ldab/split-or-not-keyboard/.github/2023-12-31_12-59.png

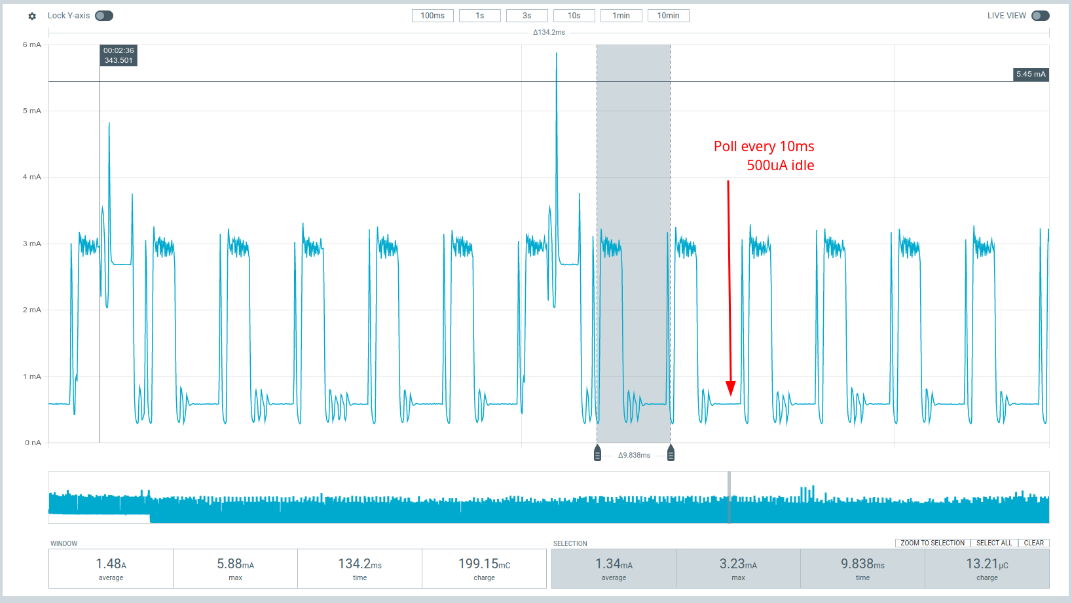
.github/2023-12-31_12-59.png
