ldab/split-or-not-keyboard/.github/basic60_idle_int.png

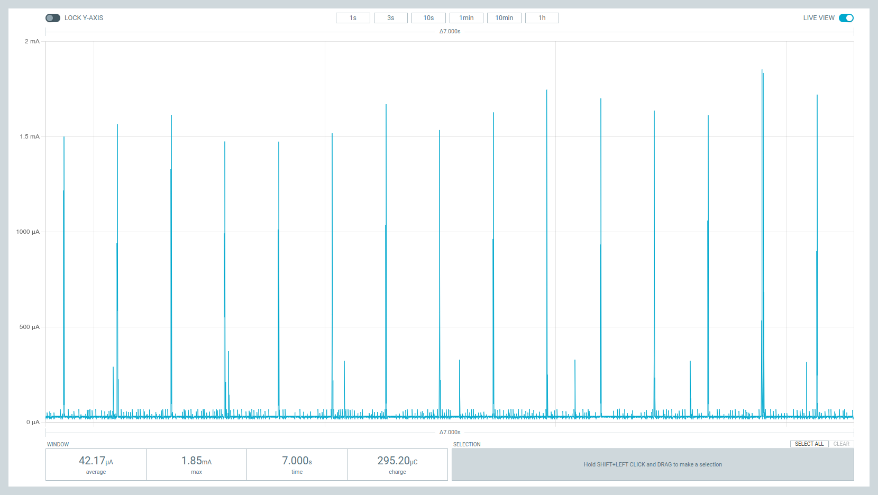
.github/basic60_idle_int.png
