ldab/split-or-not-keyboard/.github/ppk-20240103T102012.png

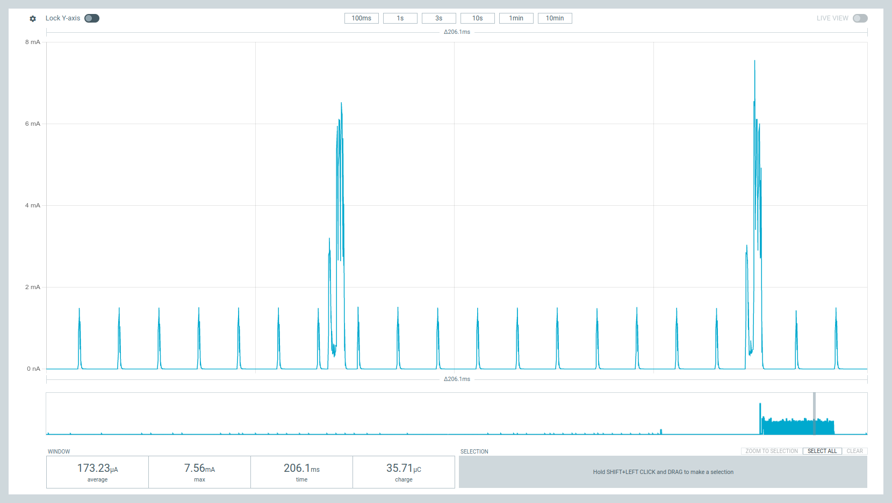
.github/ppk-20240103T102012.png
