ldab/split-or-not-keyboard/.github/ppk-20240103T121507.png

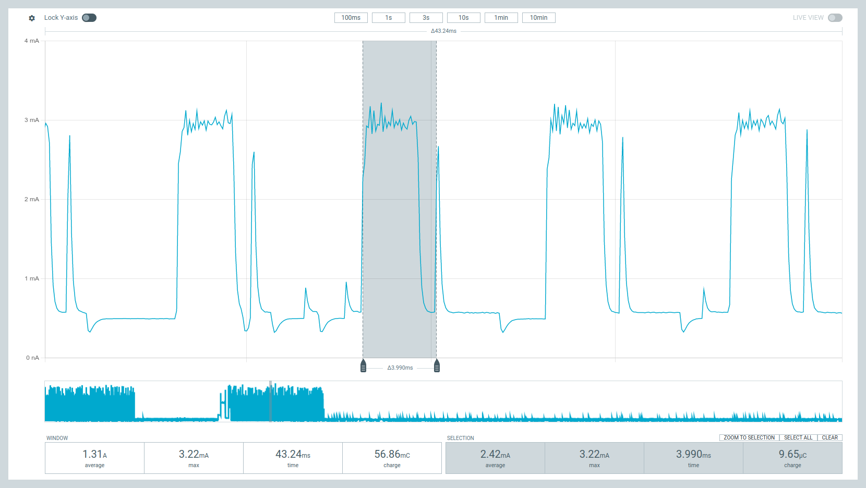
.github/ppk-20240103T121507.png
