ldab/split-or-not-keyboard/basic/3D/basic60-3D_top.png

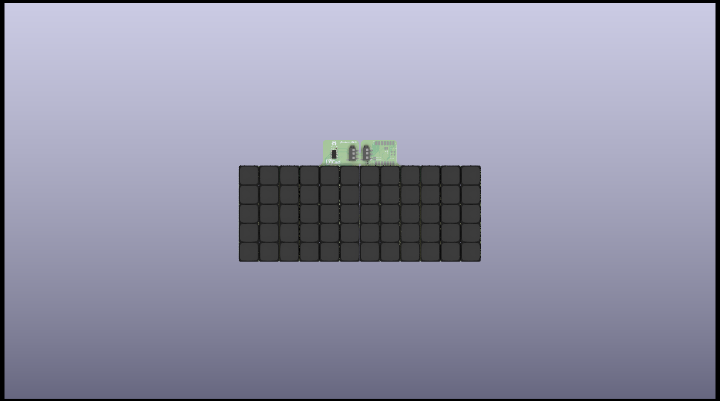
basic/3D/basic60-3D_top.png
