ldab/split-or-not-keyboard/basic/PCB/2D_render/jlcpcb_green_enig/basic60-bottom.png

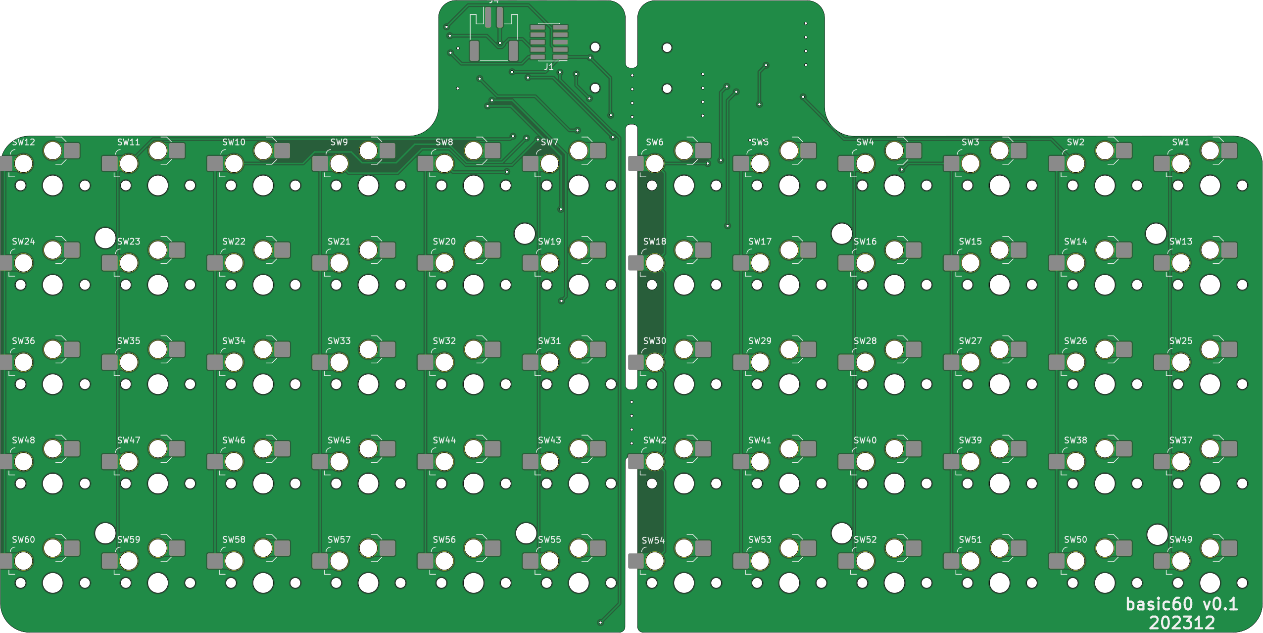
basic/PCB/2D_render/jlcpcb_green_enig/basic60-bottom.png
