ldab/split-or-not-keyboard/ergo/PCB/2D_render/jlcpcb_green_enig/ergo56-bottom.png

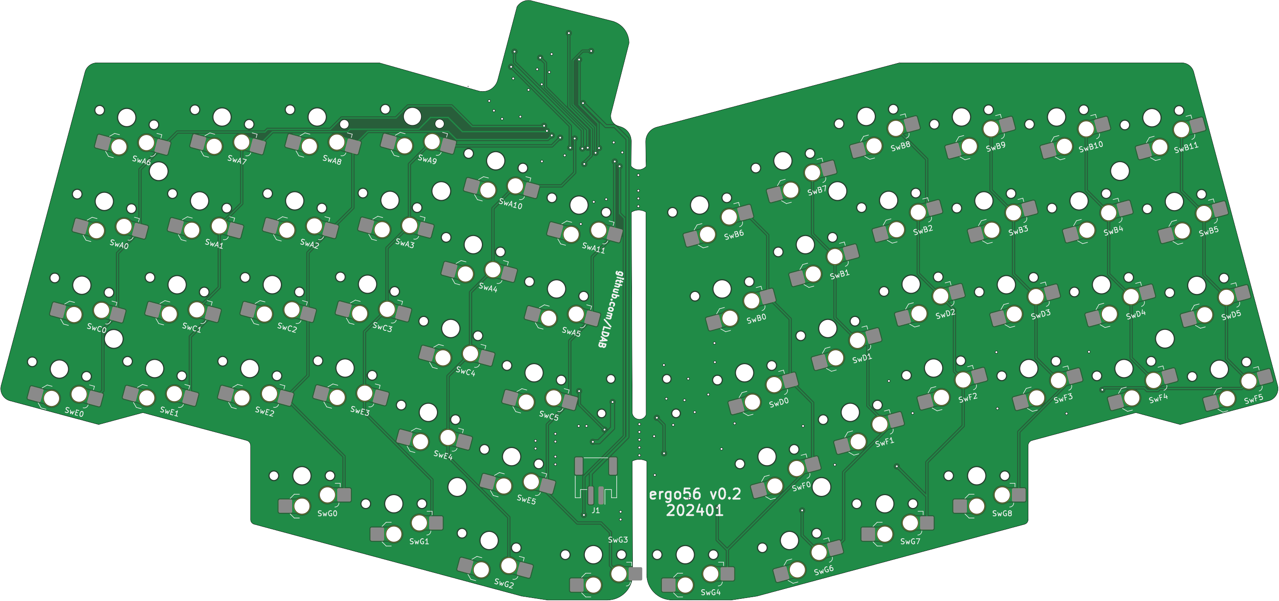
ergo/PCB/2D_render/jlcpcb_green_enig/ergo56-bottom.png
