ldab/split-or-not-keyboard/ergo/PCB/PNG/ergo56-assembly_page_02.png

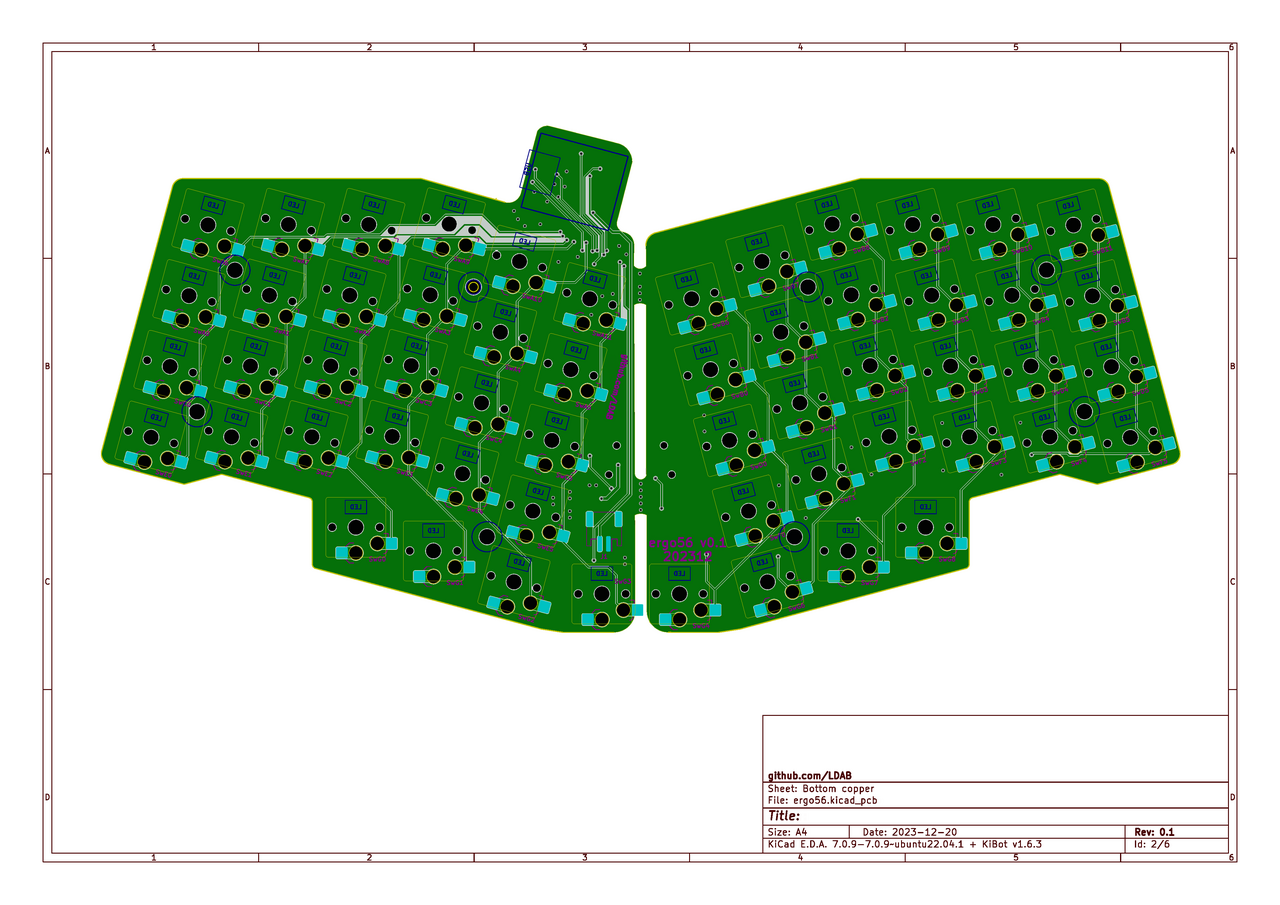
ergo/PCB/PNG/ergo56-assembly_page_02.png
