ldab/split-or-not-keyboard/ergo/PCB/PDF/02/ergo56.pdf

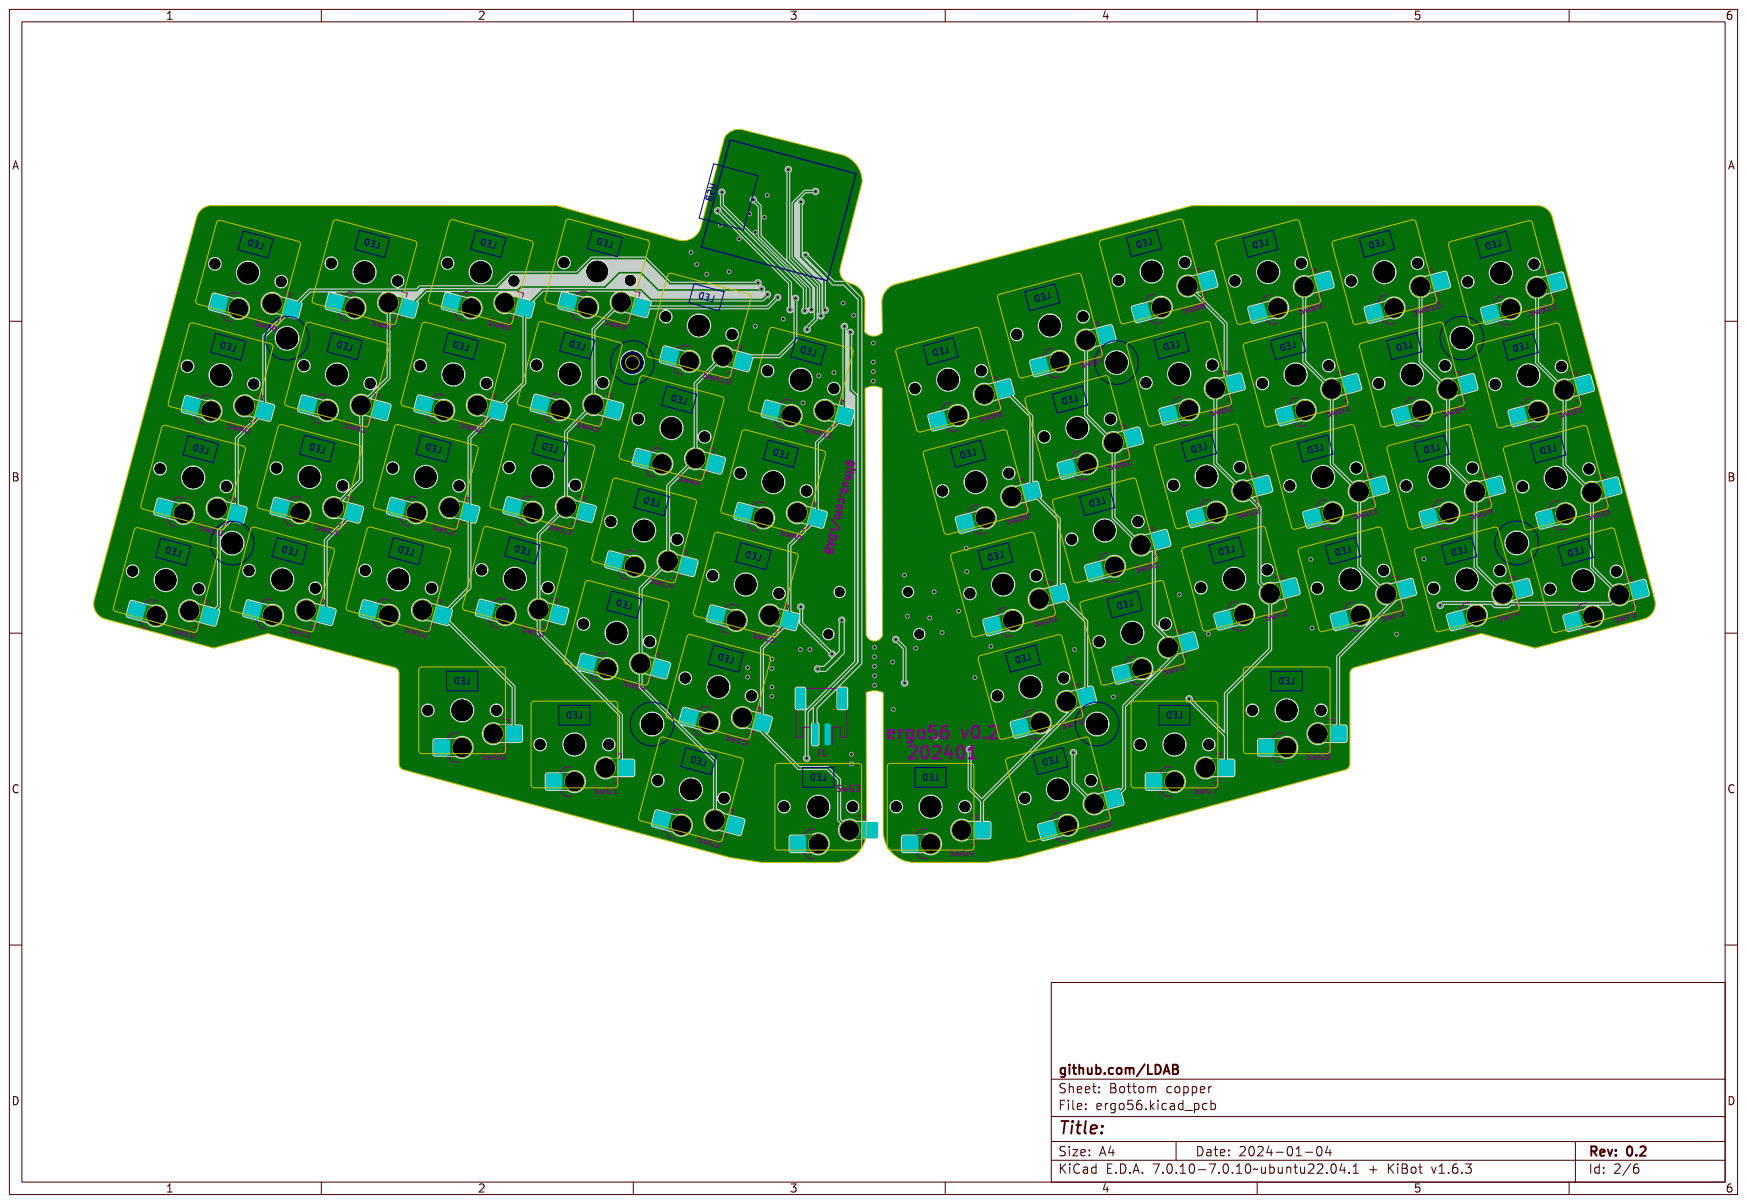
[picture p36: page 1]
ergo56 v0.2 202401; SwE0; SwE1; SwE2; SwE3; SwD3 SwD4 SwD5; SwD1; SwD0; SwC5; SwB0 SwD2; SwC4; SwC0; SwC1; SwC2; SwC3; SwB5; SwG2; SwB4; SwA0; SwA4; SwA3; SwB1; SwF0; SwA1; SwB2 SwB3; SwF2 SwF3 SwF4 SwF5; SwF1; SwE5; SwE4; SwA2; SwA5; SwG1; SwG6; SwG7; SwG4; SwG0; SwA6; SwA7; SwB9; SwG8; SwB11; SwA9; SwA11; SwB7; SwB8 SwB10; SwA8; SwA10; SwG3; SwB6; USB; Size: A4; Rev: 0.2; Date: 2024-01-04

github.com/LDAB
Sheet: Bottom copper
File: ergo56.kicad_pcb
Title:
KiCad E.D.A. 7.0.10-7.0.10~ubuntu22.04.1 + KiBot v1.6.3
