ldab/split-or-not-keyboard/ergo/PCB/PDF/04/ergo56.pdf

USB; LED LED; LED; Sheet:; Front courtyard area; Size: A4; Rev: 0.2; KiCad; E.D.A. 7.0.10-7.0.10~ubuntu22.04.1; + KiBot v1.6.3; Date: 2024-01-04

LED LED LED

github.com/LDAB
File: ergo56.kicad_pcb
Title:
