ldab/split-or-not-keyboard/ergo/PCB/PNG/02/ergo56.pdf

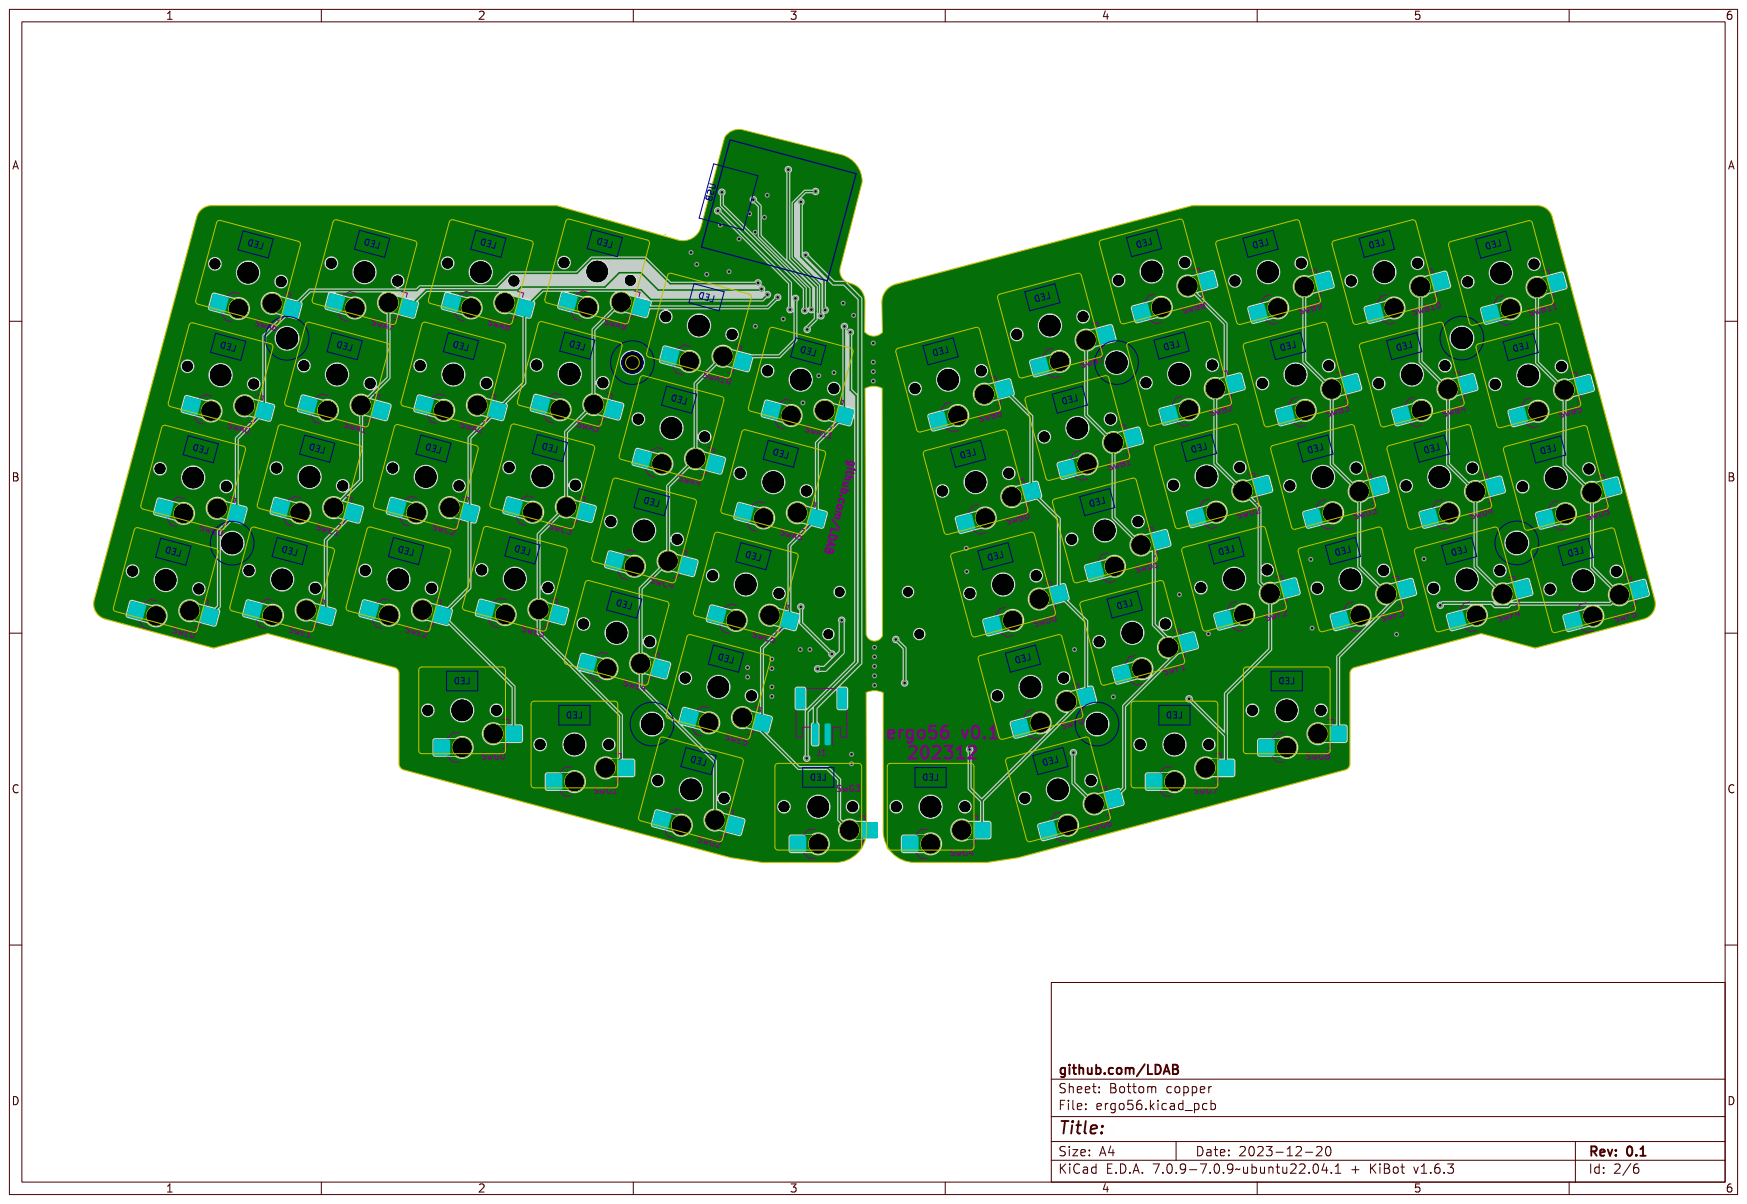
[picture p37: page 1]
USB; LED LED; LED; Size: A4; Rev: 0.1; Date: 2023-12-20

LED LED LED

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
