ldab/split-or-not-keyboard/ergo/PCB/PNG/06/ergo56_joined.pdf

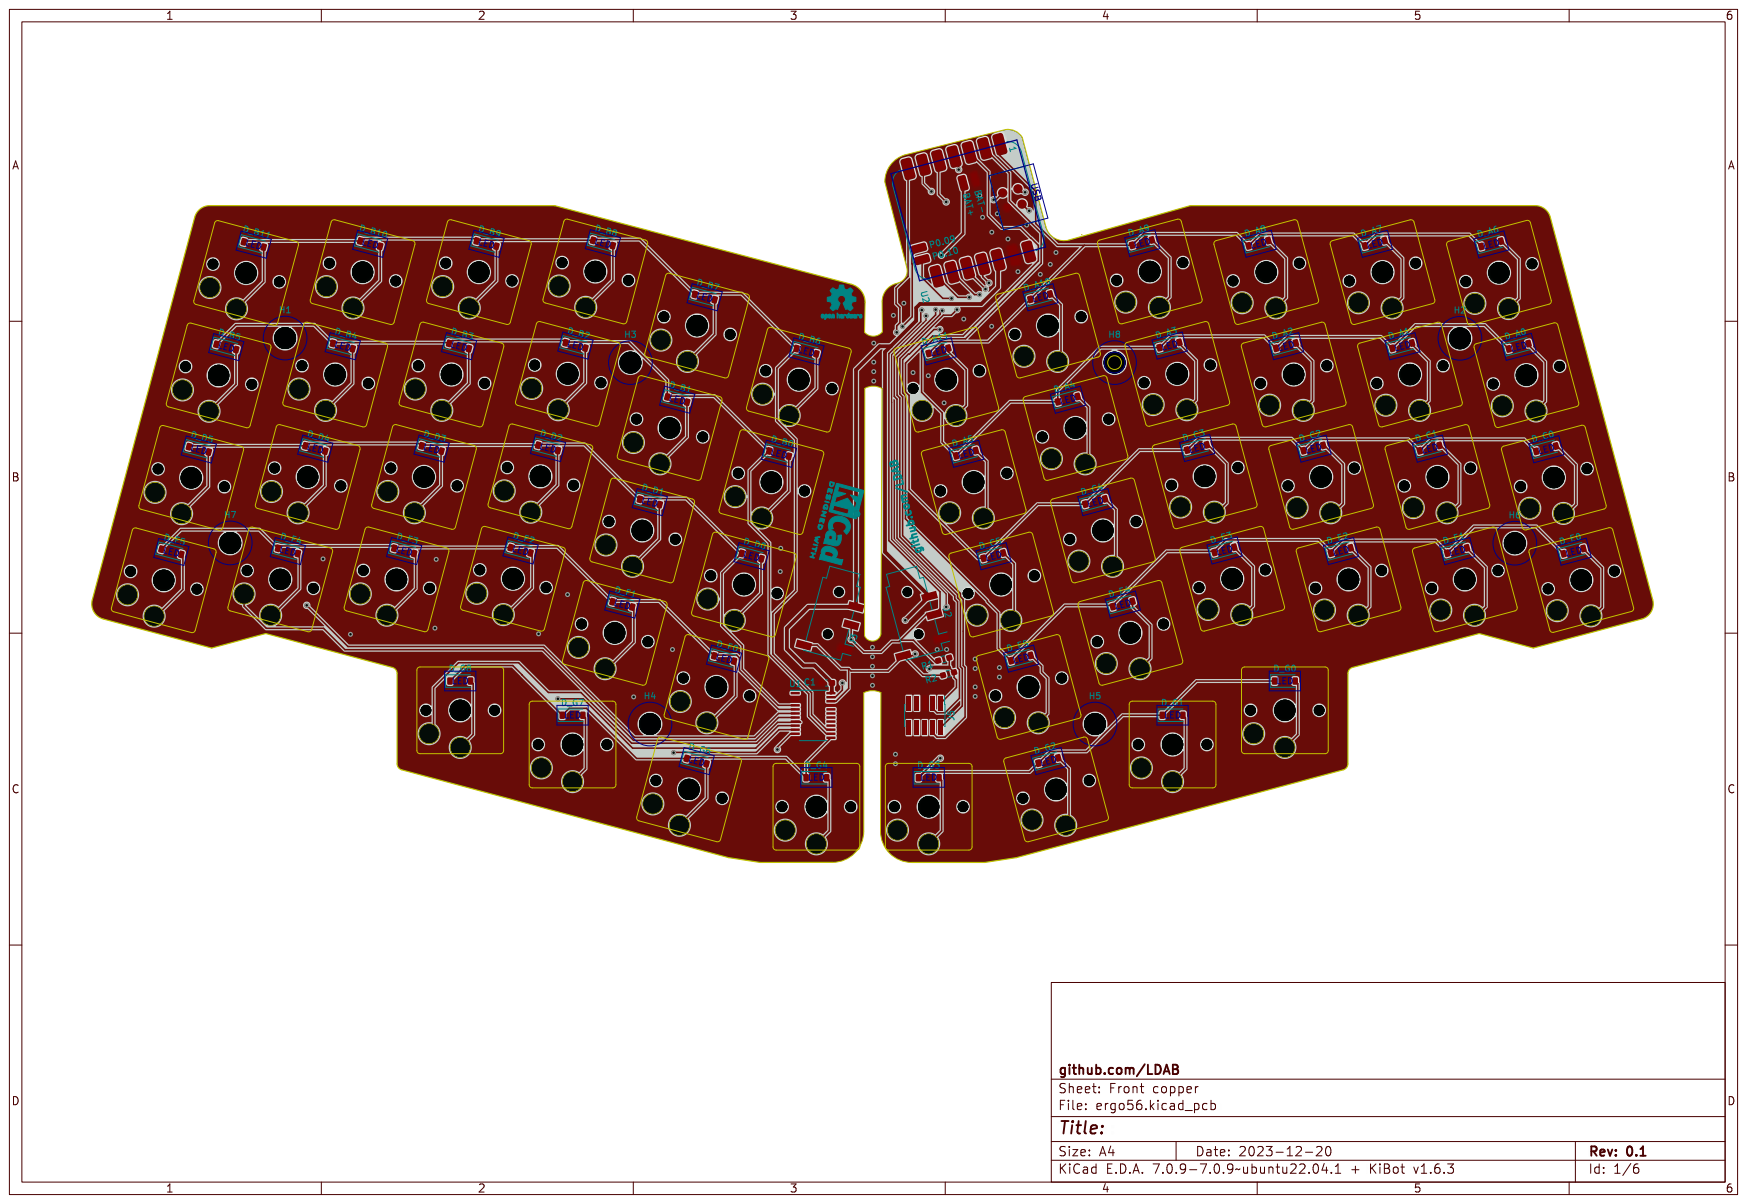
[picture p38: page 1]

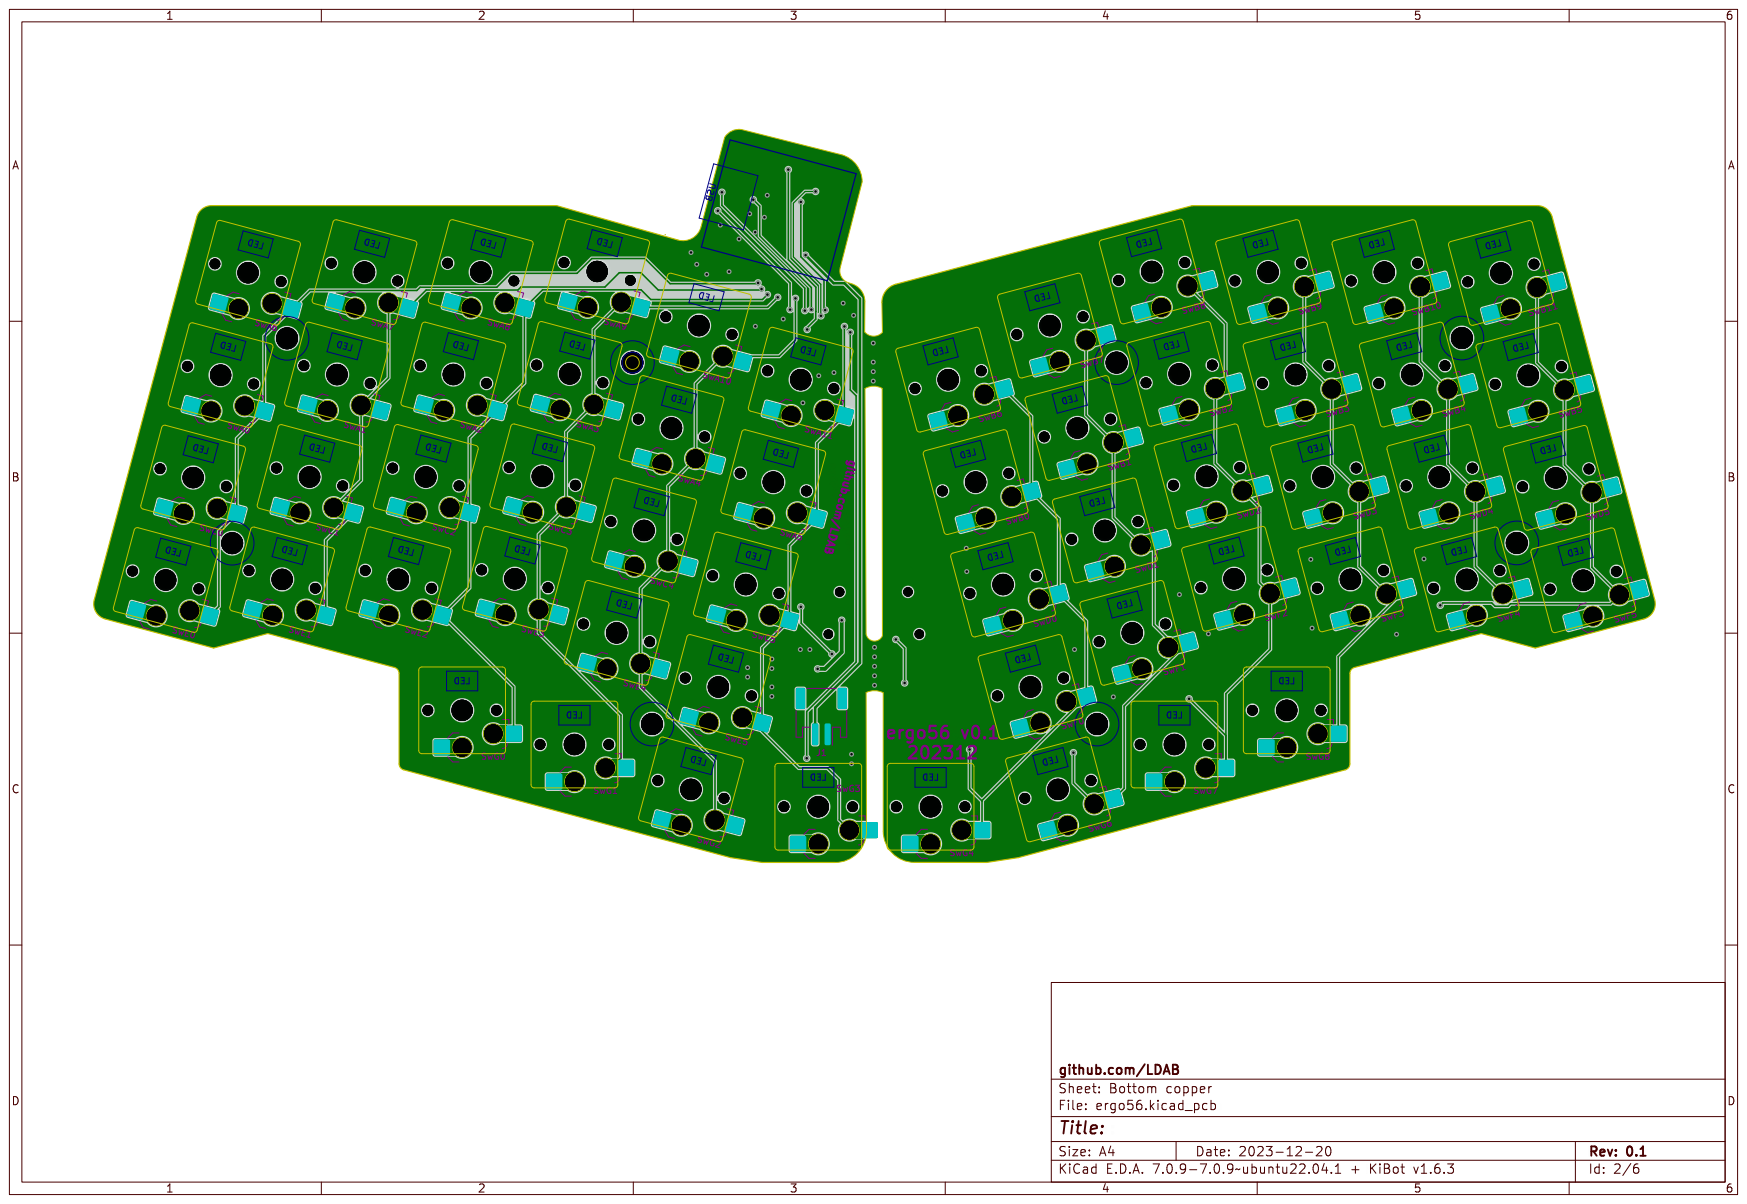
[picture p39: page 2]
USB; LED LED; LED

LED LED LED

github.com/LDAB
Sheet: Bottom copper
File: ergo56.kicad_pcb
Title:

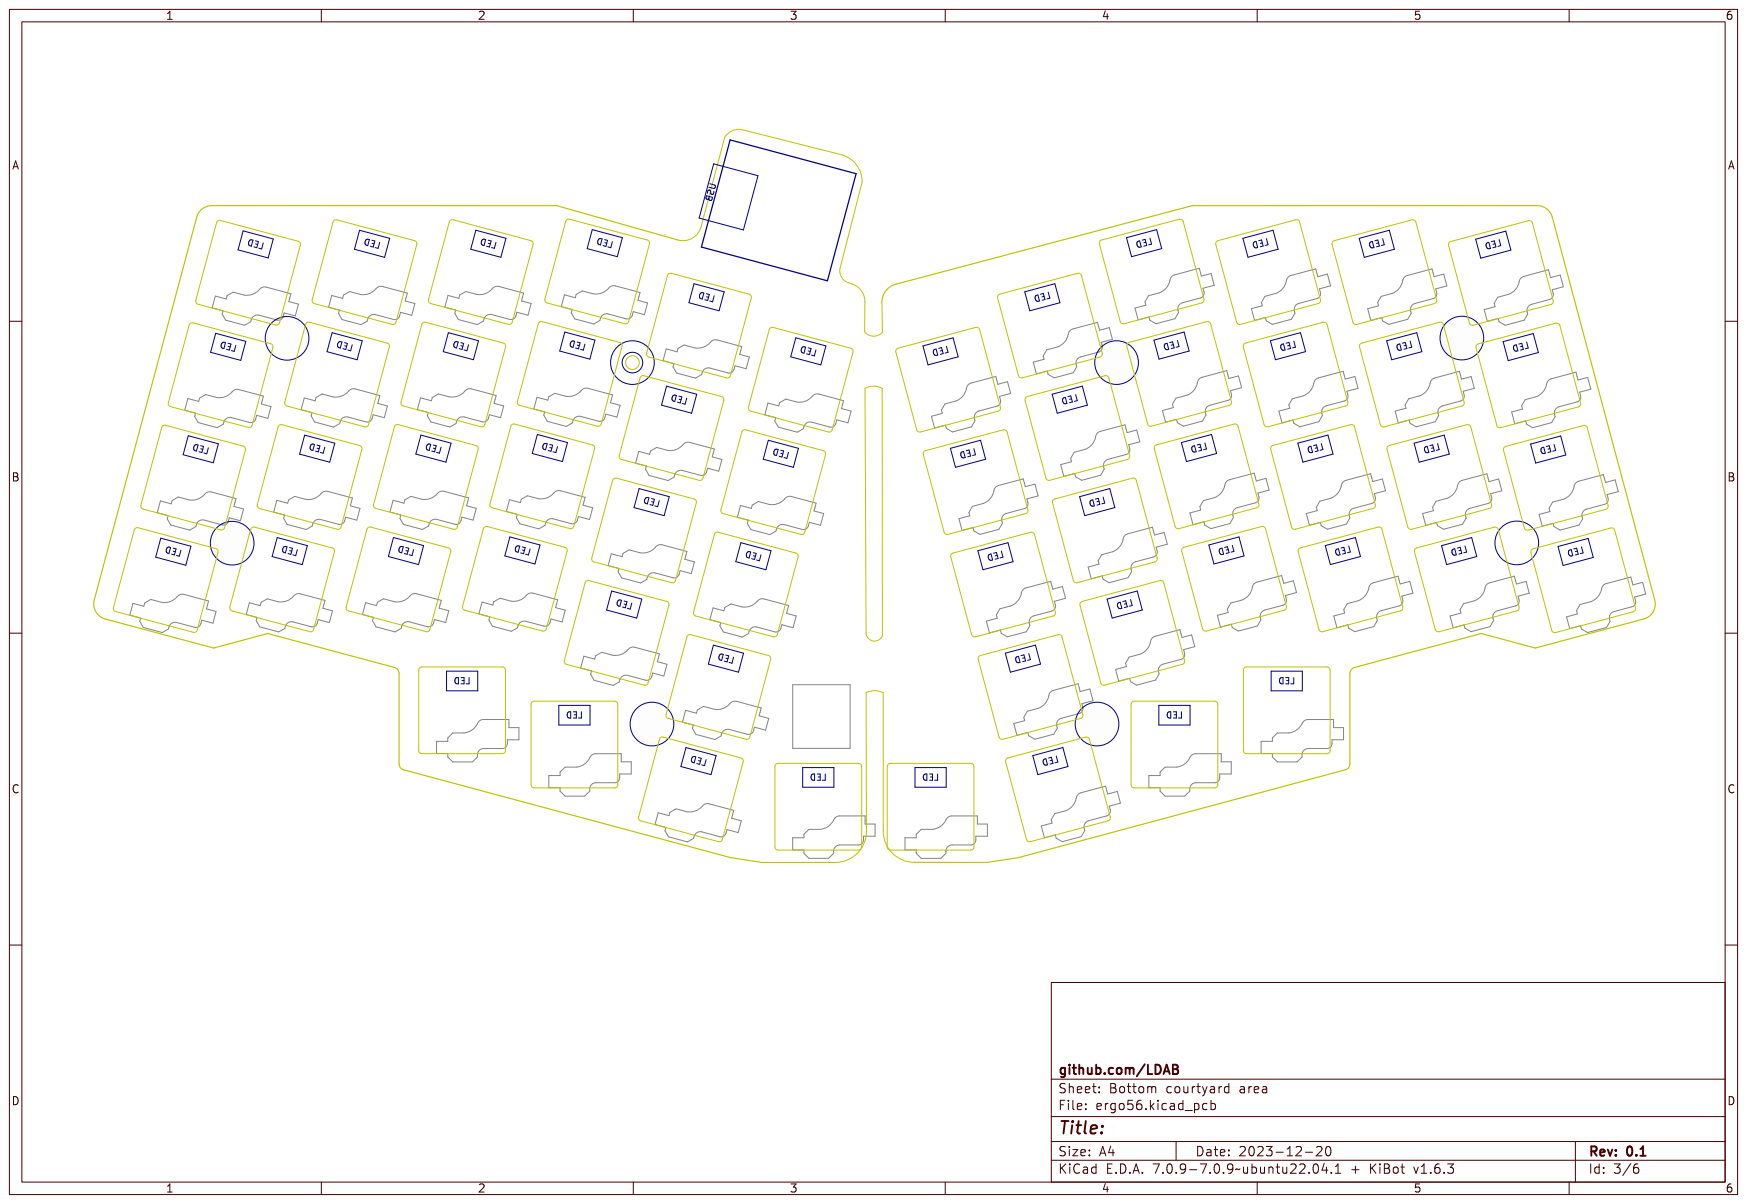
[picture p40: page 3]
USB; LED LED; LED; Sheet:; Bottom courtyard area

LED LED LED

github.com/LDAB
File: ergo56.kicad_pcb
Title:

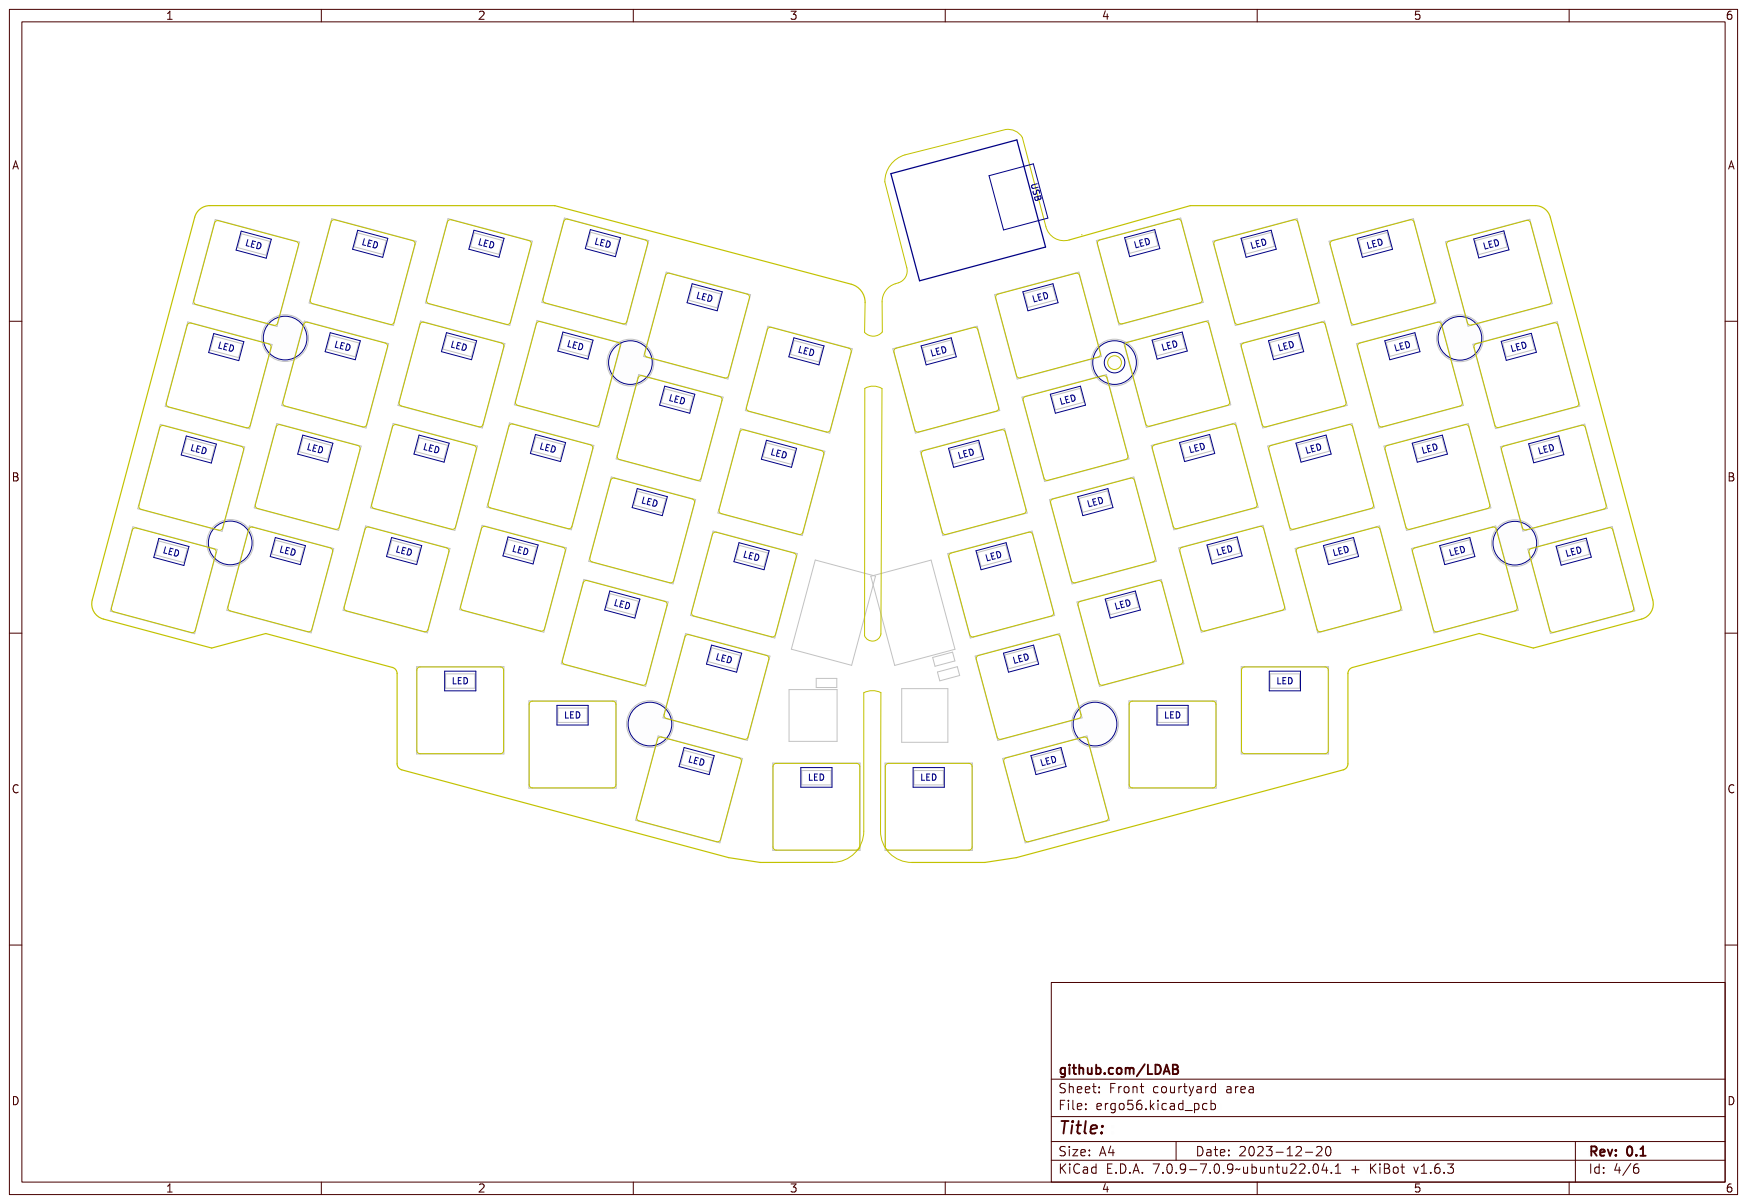
[picture p41: page 4]
USB; LED LED; LED; Sheet:; Front courtyard area

LED LED LED

github.com/LDAB
File: ergo56.kicad_pcb
Title:

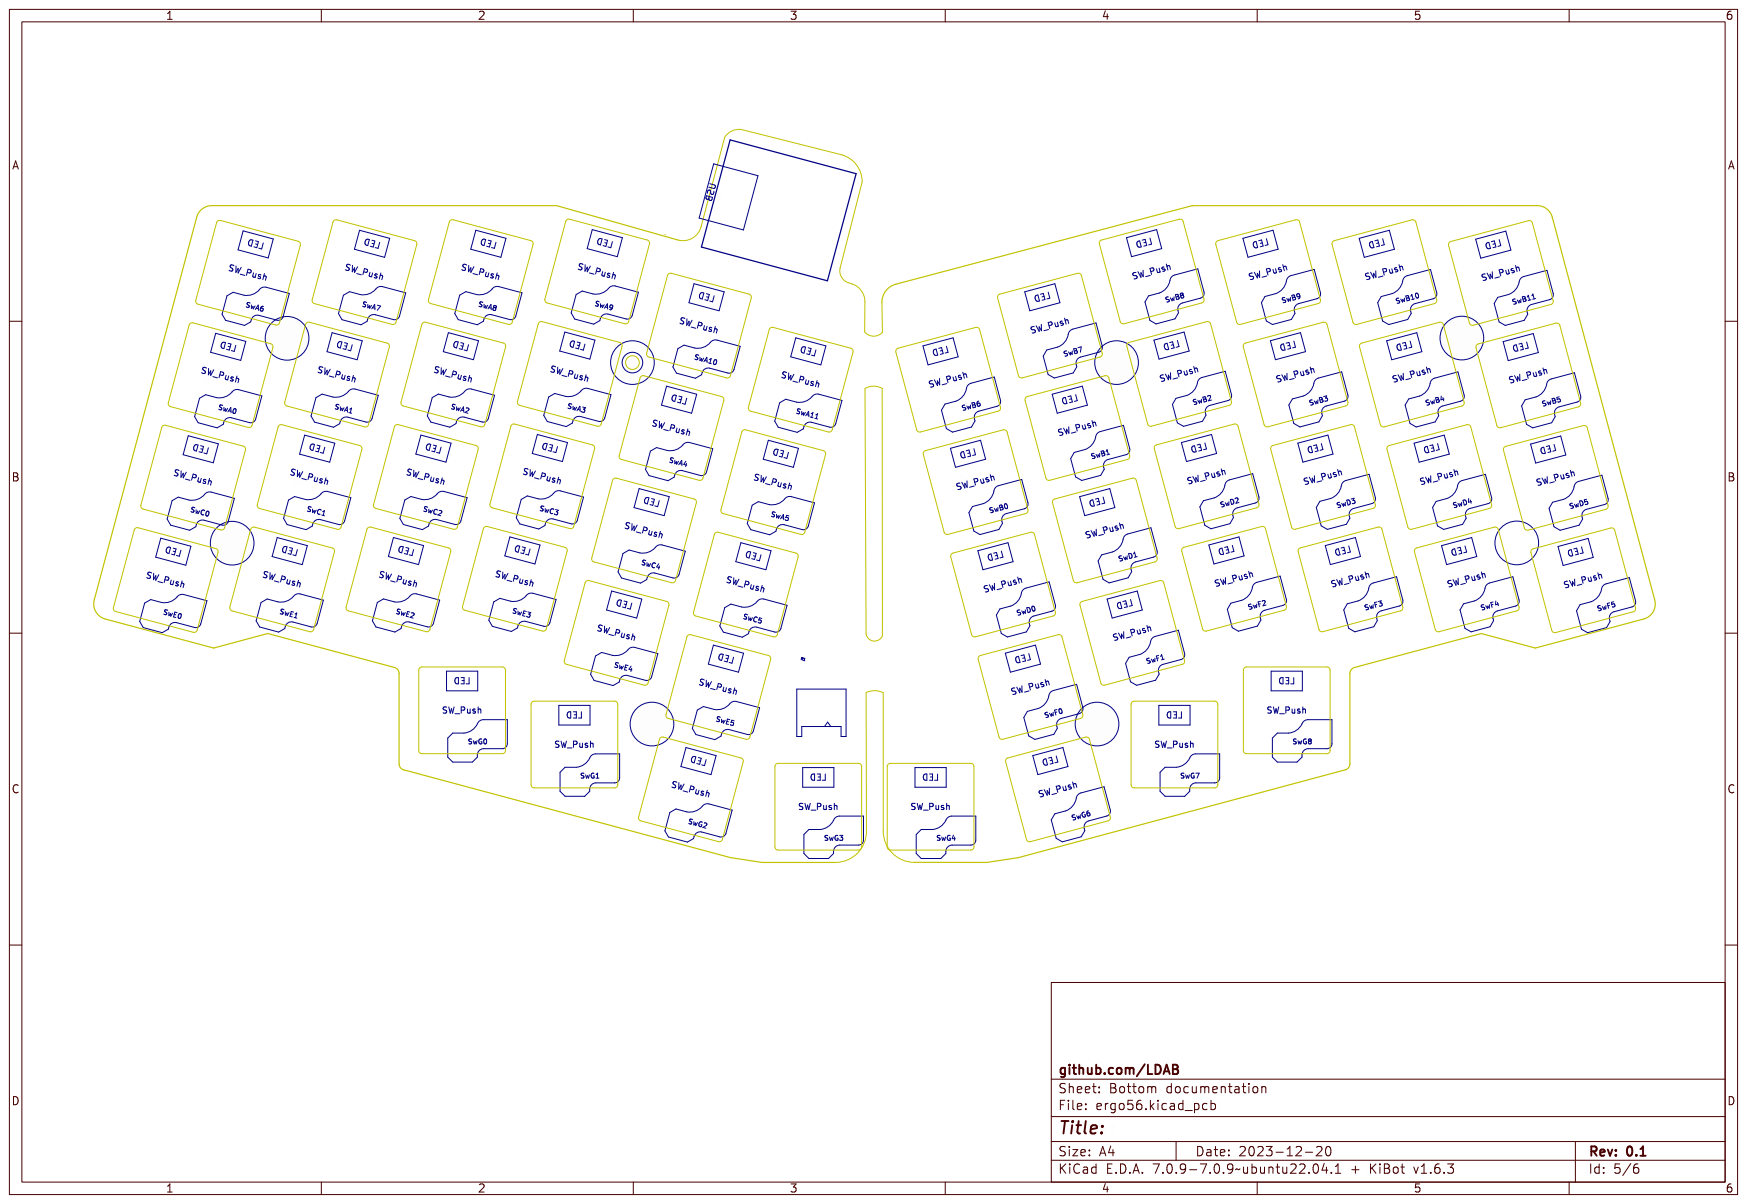
[picture p42: page 5]
USB; LED LED; LED

LED LED LED

github.com/LDAB
Sheet: Bottom documentation
File: ergo56.kicad_pcb
Title:

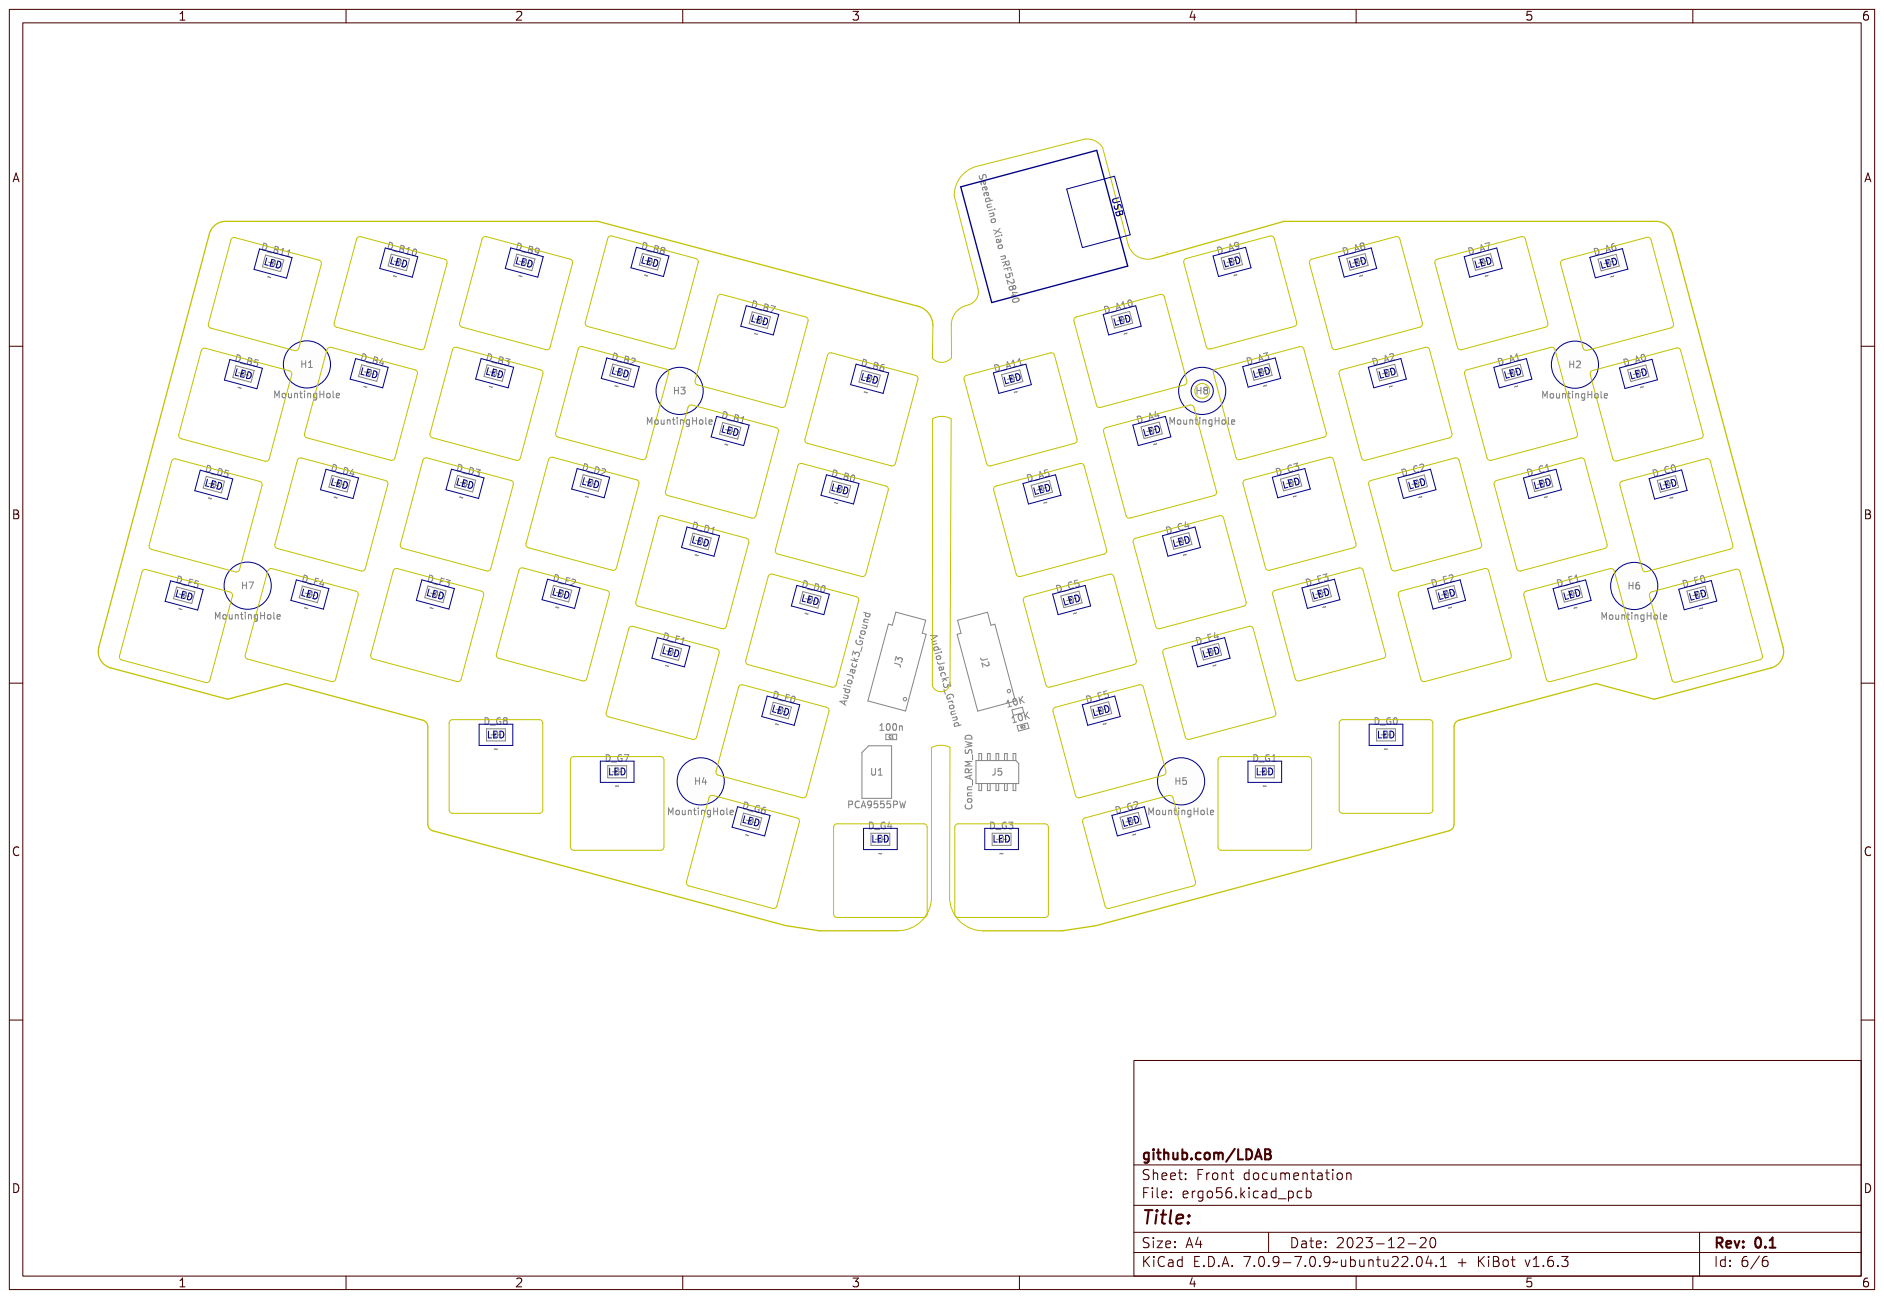
[picture p43: page 6]
D_E4 AudioJack3_Ground J3; MountingHole; Conn_ARM_SWD J5; AudioJack3_Ground; PCA9555PW; Seeeduino Xiao nRF52840; USB; LED LED; LED

LED LED LED

github.com/LDAB
Sheet: Front documentation
File: ergo56.kicad_pcb
Title:
