ldab/split-or-not-keyboard/basic/PCB/PDF/05/basic60.pdf

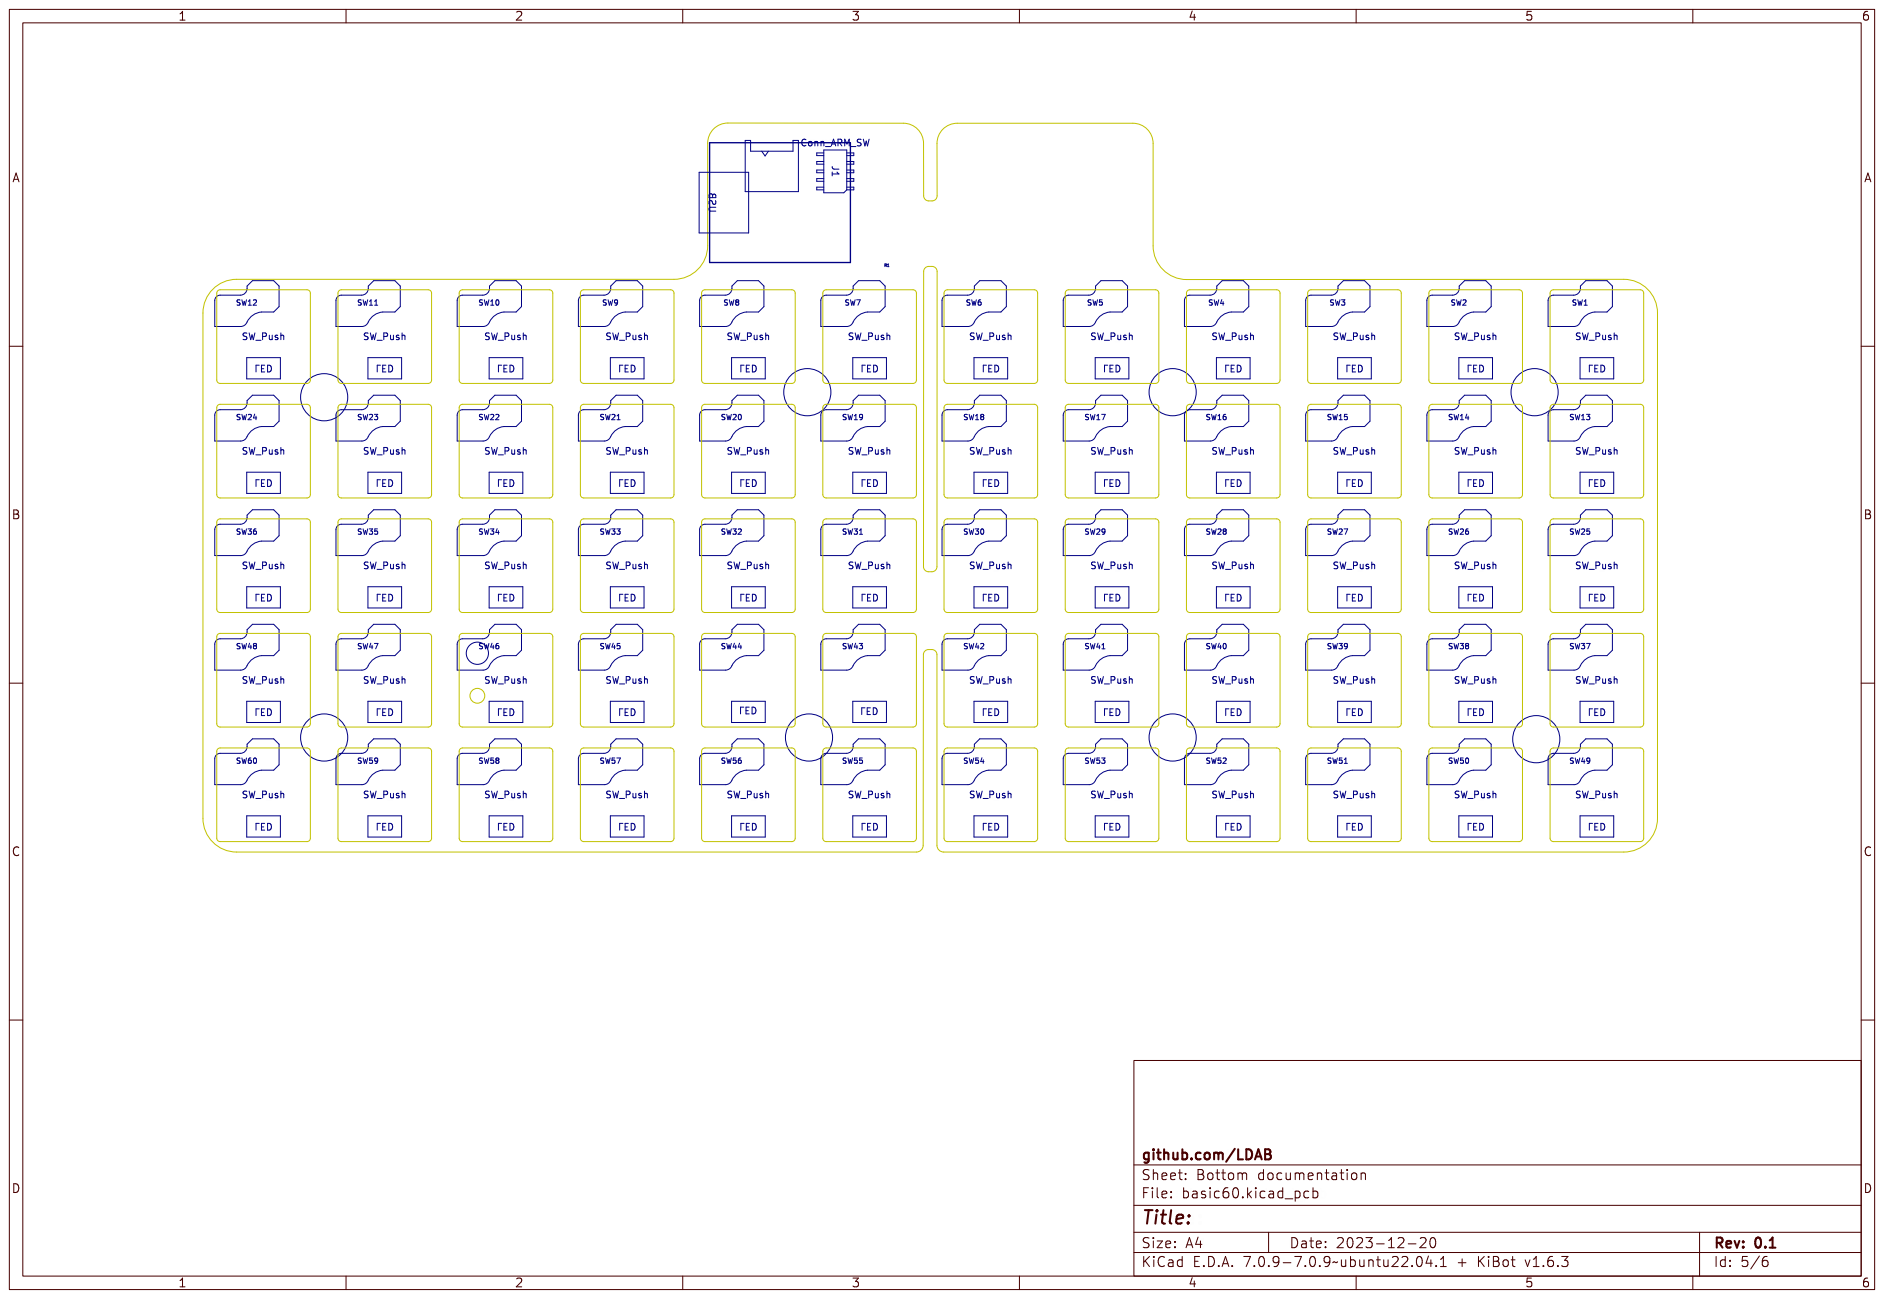
[picture p45: page 1]
