ldab/split-or-not-keyboard/basic/PCB/PDF/06/basic60.pdf

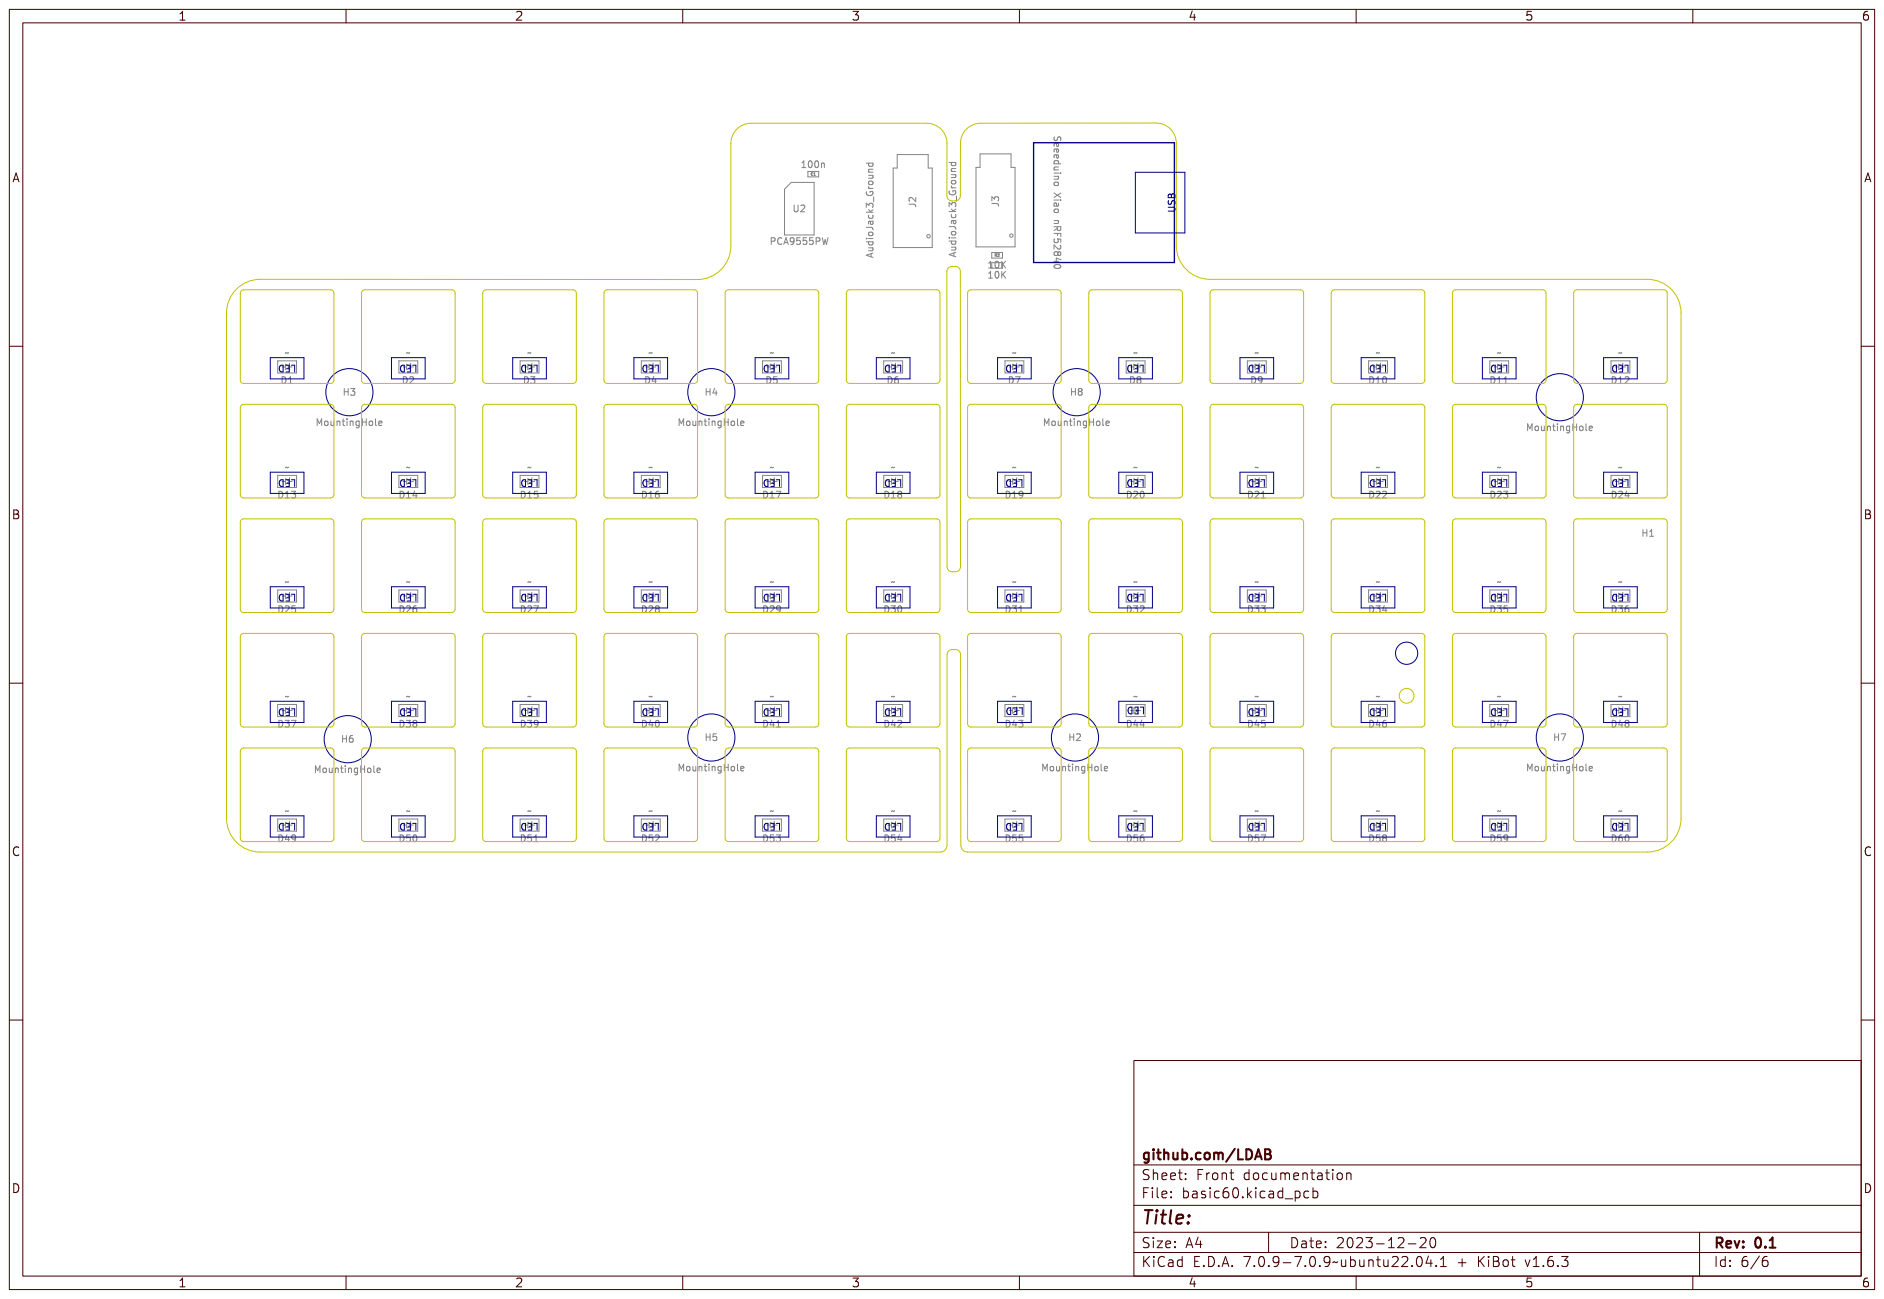
[picture p46: page 1]
